eduardocasino/kim-1-mtu-motherboard/kim-1-aux-card-esp/images/kim-1-aux-card-esp-back.png

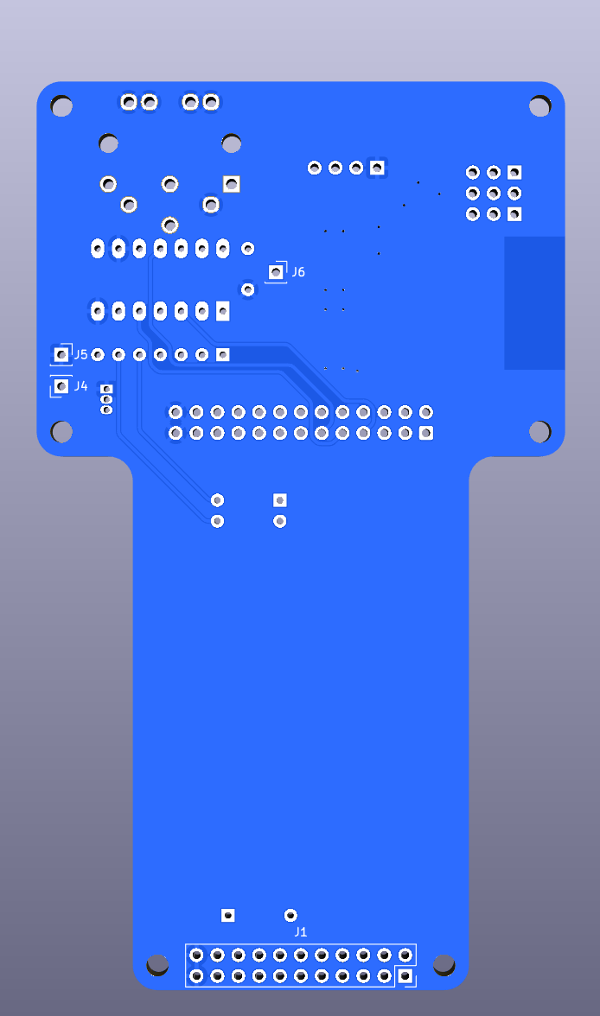
kim-1-aux-card-esp/images/kim-1-aux-card-esp-back.png
